dalethomas81/YetiMon/media/build/microcontroller-close-up.jpeg

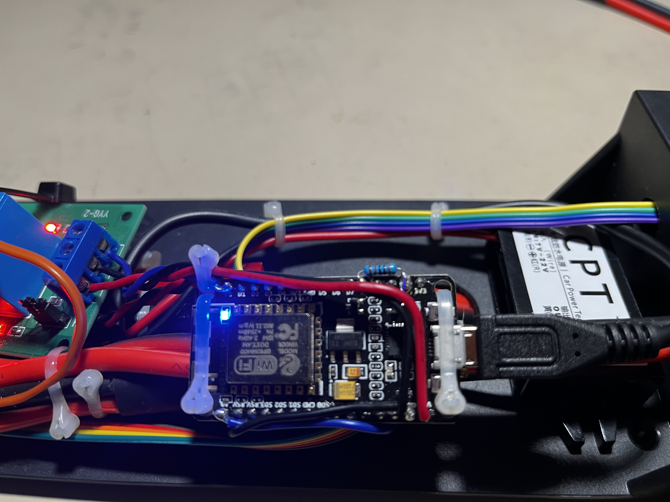
media/build/microcontroller-close-up.jpeg
