dalethomas81/YetiMon/media/build/relay-close-up.jpeg

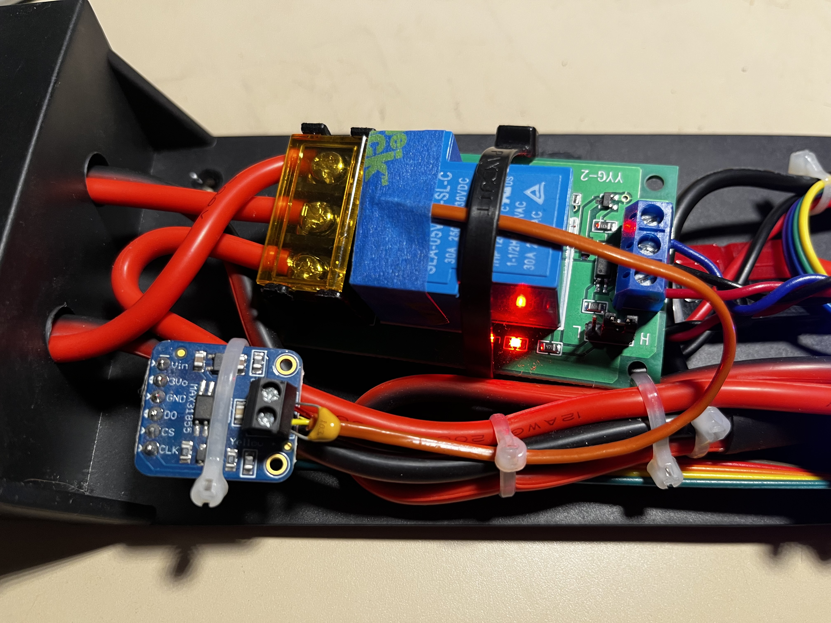
media/build/relay-close-up.jpeg
