dalethomas81/YetiMon/media/build/rool-solar.jpeg

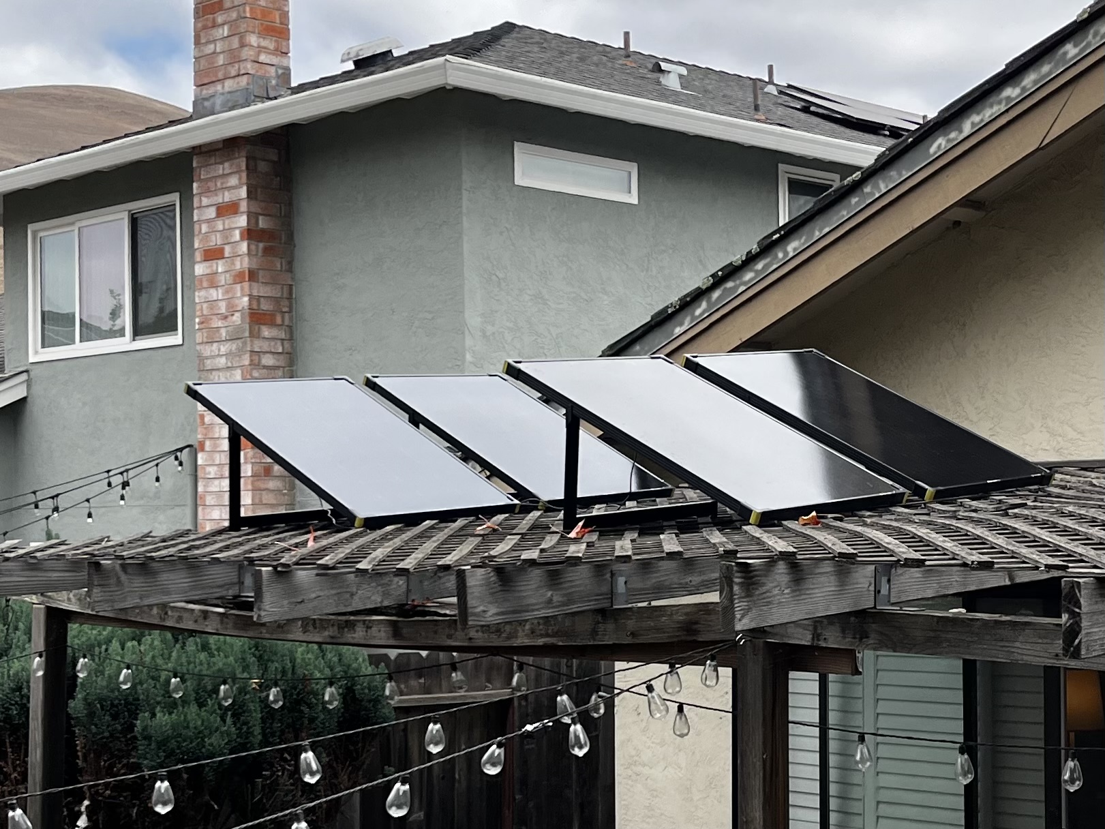
media/build/rool-solar.jpeg
