dalethomas81/YetiMon/media/build/top-down.jpeg

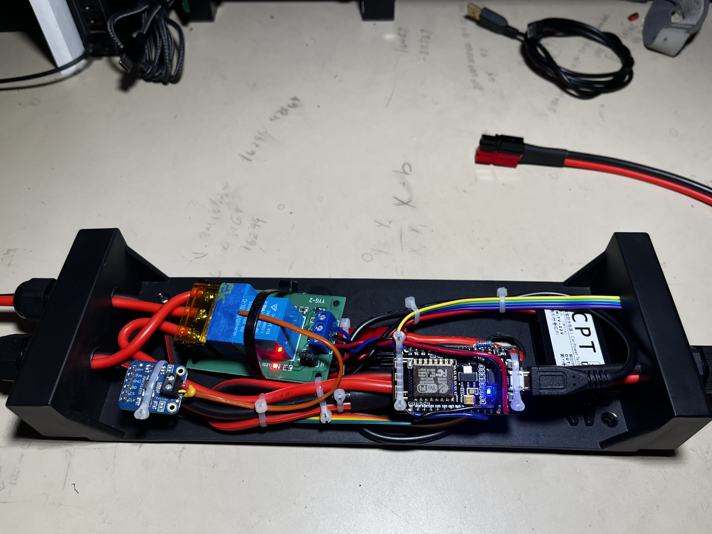
media/build/top-down.jpeg
