dalethomas81/YetiMon/source/cad/fusion-360/YetiMon/main.sch

## EAGLE design source/cad/fusion-360/YetiMon/main.sch (2022-10-27)

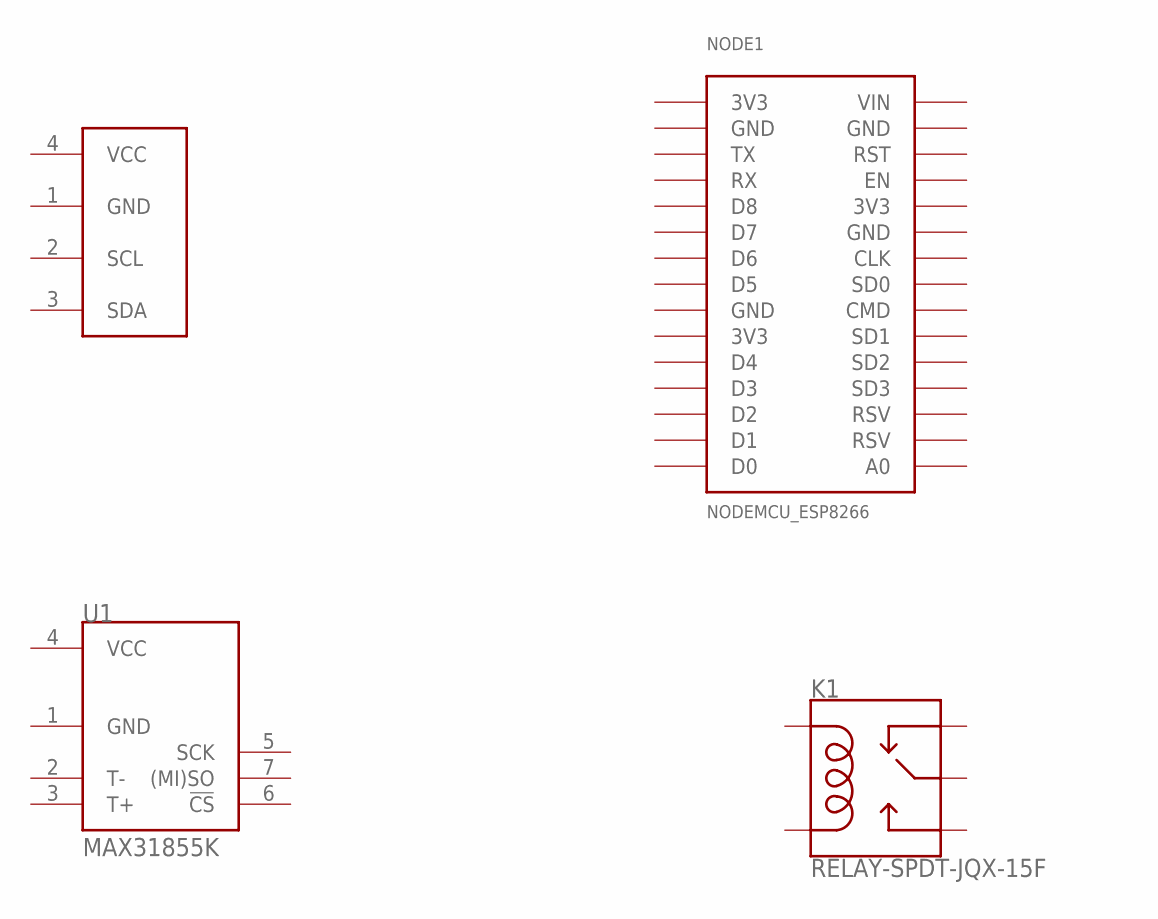
[picture p24: schematic main.sch]

Parts:
K1: RELAY-SPDT-JQX-15F; RELAY-T90
NODE1: NODEMCU_ESP8266
U1: MAX31855K; SO08
U$1: I2C_OLED; I2C_OLED_PACKAGE
