dalethomas81/YetiMon/media/build/input-cables.jpeg

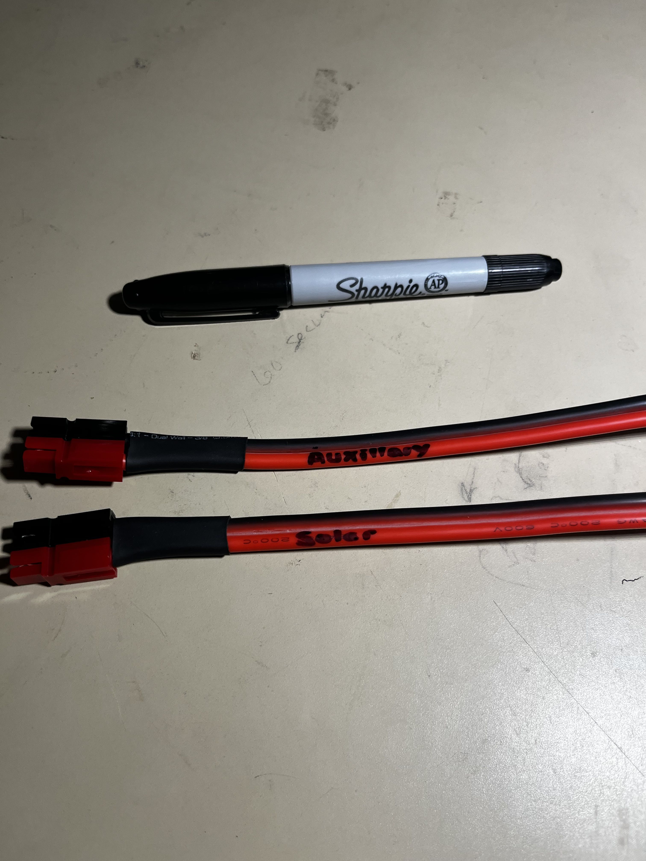
media/build/input-cables.jpeg
