dalethomas81/YetiMon/media/build/installed-isometric.jpeg

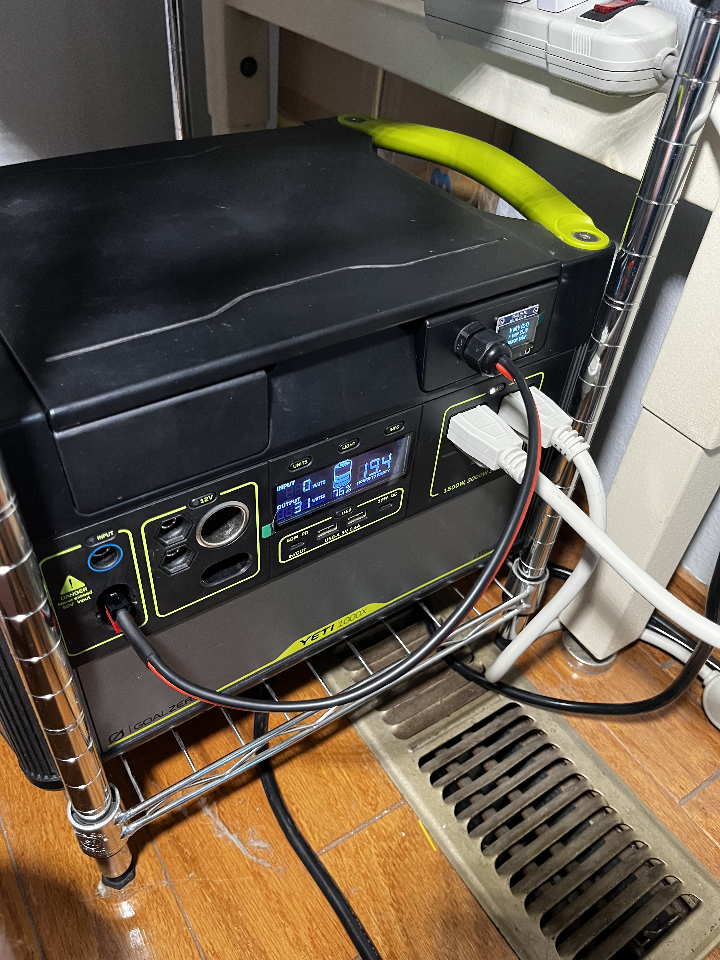
media/build/installed-isometric.jpeg
