dalethomas81/YetiMon/media/build/oled-display.jpeg

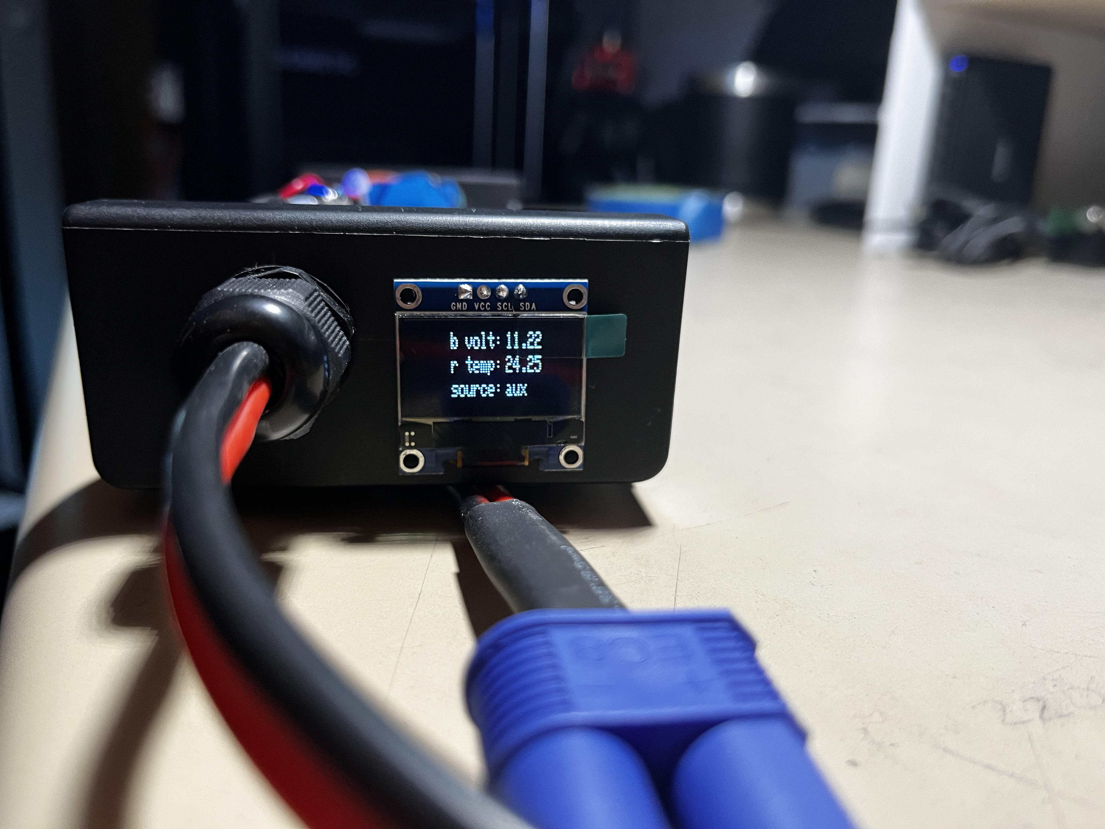
media/build/oled-display.jpeg
