dalethomas81/YetiMon/media/build/side-profile-with-cover.jpeg

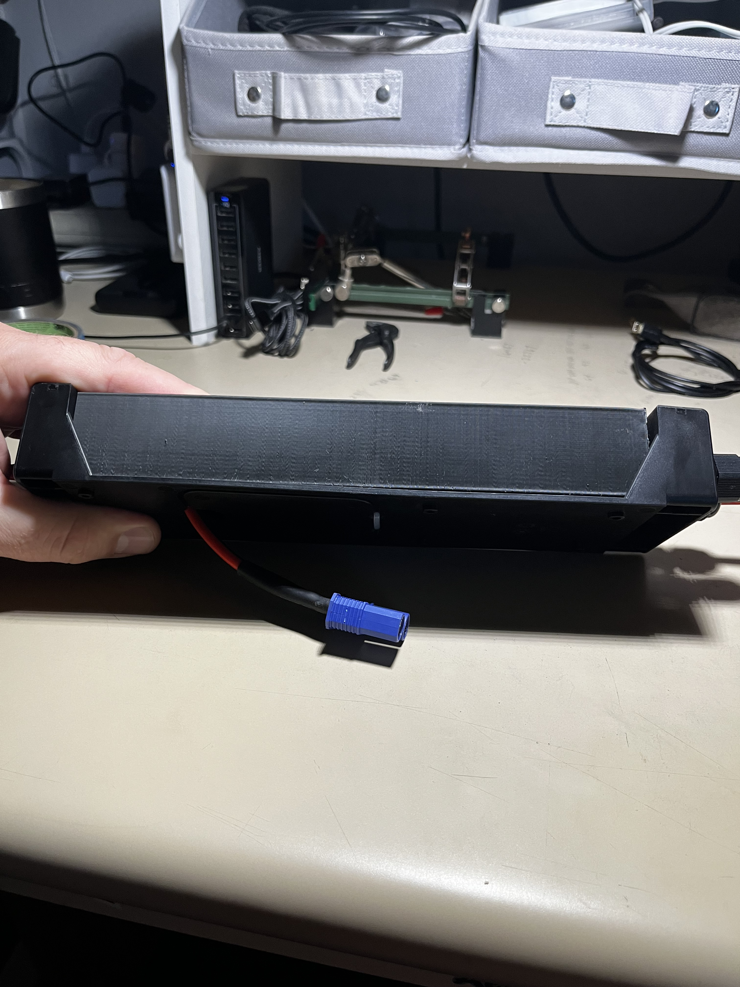
media/build/side-profile-with-cover.jpeg
