dalethomas81/YetiMon/media/build/voltage-devider.jpeg

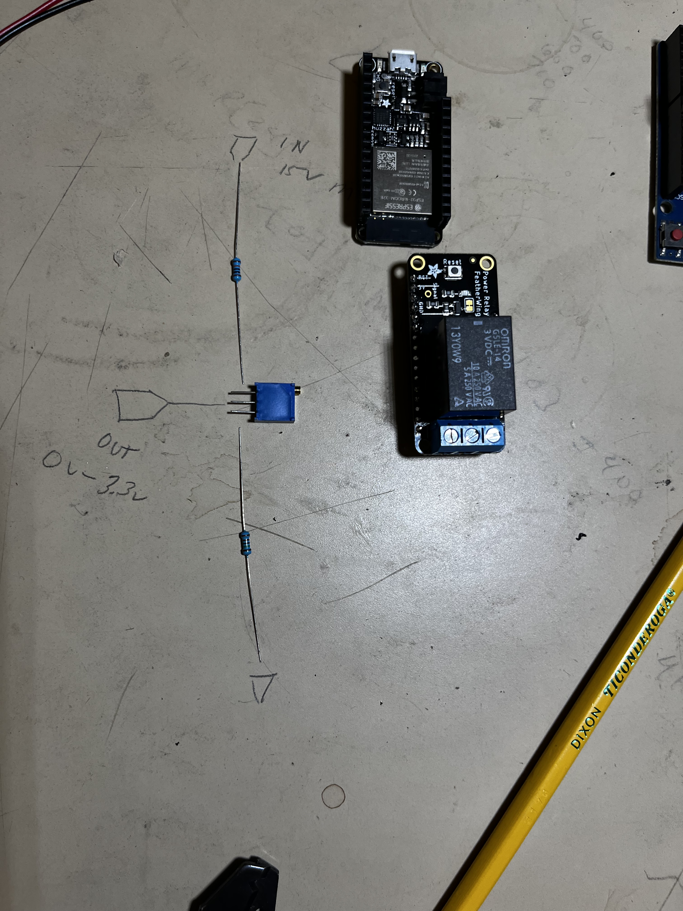
media/build/voltage-devider.jpeg
